Fisers/Weather-station/hardware/Radiation shield/Daniels_Base_Clamp.stl

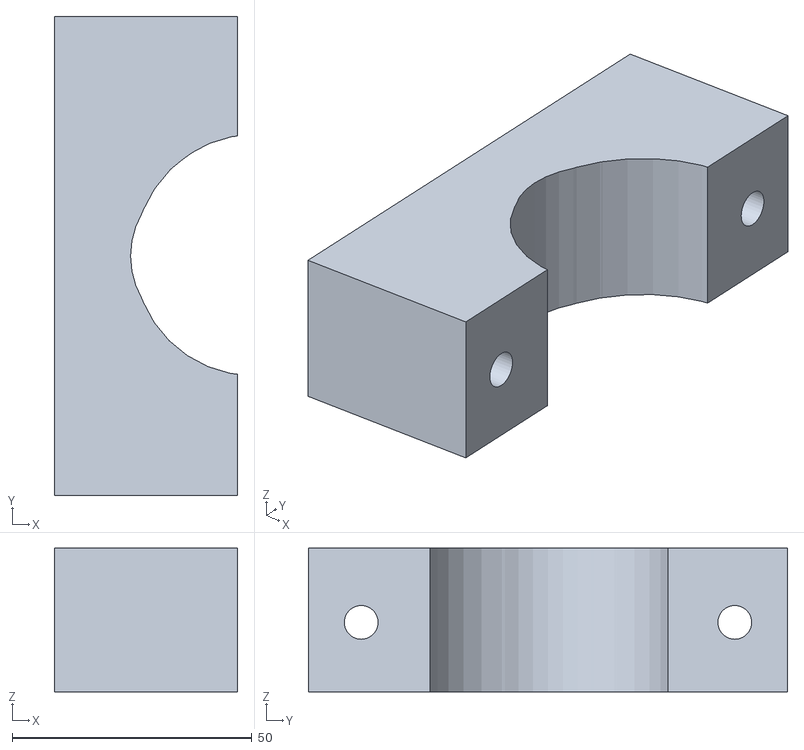
[picture p15: CAD file, 2019-08-27]
hardware/Radiation shield/Daniels_Base_Clamp.stl
38.3 x 100.0 x 30.0
