Fisers/Weather-station/software/Meteorological Station/Meteorological Station/includes/RTC/rtc.c

/***************************************************************************************************
                                   ExploreEmbedded    
****************************************************************************************************
 * File:   rtc.c
 * Version: 15.0
 * Author: ExploreEmbedded
 * Website: http://www.exploreembedded.com/wiki
 * Description: Contains the library functions for RTC-Ds1307 date and time read write

The libraries have been tested on ExploreEmbedded development boards. We strongly believe that the 
library works on any of development boards for respective controllers. However, ExploreEmbedded 
disclaims any kind of hardware failure resulting out of usage of libraries, directly or indirectly.
Files may be subject to change without prior notice. The revision history contains the information 
related to updates. 


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
Errors and omissions should be reported to codelibraries@exploreembedded.com
***************************************************************************************************/



/***************************************************************************************************
                             Revision History
****************************************************************************************************
15.0: Initial version 
***************************************************************************************************/

#include "rtc.h"
#include "../I2C/i2cmaster.h"
#include <util/delay.h>





/***************************************************************************************************
                         void RTC_Init(void)
****************************************************************************************************
 * I/P Arguments: none.
 * Return value    : none

 * description :This function is used to Initialize the Ds1307 RTC.
***************************************************************************************************/
void RTC_Init(void)
{
	rtc_I2C_Start();

    i2c_write(C_Ds1307WriteMode_U8);        // Connect to DS1307 by sending its ID on I2c Bus
    i2c_write(C_Ds1307ControlRegAddress_U8);// Select the Ds1307 ControlRegister to configure Ds1307

    i2c_write(0x00);                        // Write 0x00 to Control register to disable SQW-Out

    i2c_stop();                             // Stop I2C communication after initializing DS1307
}














/***************************************************************************************************
                    void RTC_SetDateTime(rtc_t *rtc)
****************************************************************************************************
 * I/P Arguments: rtc_t *: Pointer to structure of type rtc_t. Structure contains hour,min,sec,day,date,month and year 
 * Return value    : none

 * description  :This function is used to update the Date and time of Ds1307 RTC.
                 The new Date and time will be updated into the non volatile memory of Ds1307.
        Note: The date and time should be of BCD format, 
             like 0x12,0x39,0x26 for 12hr,39min and 26sec.    
                  0x15,0x08,0x47 for 15th day,8th month and 47th year.                 
***************************************************************************************************/
// Convert Decimal to Binary Coded Decimal (BCD)
static uint8_t dec2bcd(uint8_t num)
{
	return ((num/10 * 16) + (num % 10));
}

void RTC_SetDateTime(rtc_t *rtc)
{
    rtc_I2C_Start();                          // Start I2C communication
	
	//i2c_write(0x00);
	//i2c_write(0x80);
    i2c_write(C_Ds1307WriteMode_U8);      // connect to DS1307 by sending its ID on I2c Bus
    i2c_write(C_Ds1307SecondRegAddress_U8); // Request sec RAM address at 00H
	
// 	i2c_write(rtc->sec);                    // Write sec from RAM address 00H
// 	i2c_write(rtc->min);                    // Write min from RAM address 01H
// 	i2c_write(rtc->hour);                    // Write hour from RAM address 02H
// 	i2c_write(rtc->weekDay);                // Write weekDay on RAM address 03H
// 	i2c_write(rtc->date);                    // Write date on RAM address 04H
// 	i2c_write(rtc->month);                    // Write month on RAM address 05H
// 	i2c_write(rtc->year);

    i2c_write(dec2bcd(rtc->sec));                    // Write sec from RAM address 00H
    i2c_write(dec2bcd(rtc->min));                    // Write min from RAM address 01H
    i2c_write(dec2bcd(rtc->hour));                    // Write hour from RAM address 02H
    i2c_write(dec2bcd(rtc->weekDay));                // Write weekDay on RAM address 03H
    i2c_write(dec2bcd(rtc->date));                    // Write date on RAM address 04H
    i2c_write(dec2bcd(rtc->month));                    // Write month on RAM address 05H
    i2c_write(dec2bcd(rtc->year));                    // Write year on RAM address 06h*/

    i2c_stop();                              // Stop I2C communication after Setting the Date
}






// Convert Binary Coded Decimal (BCD) to Decimal
static uint8_t bcd2dec(uint8_t num)
{
	return ((num/16 * 10) + (num % 16));
}


/***************************************************************************************************
                     void RTC_GetDateTime(rtc_t *rtc)
****************************************************************************************************
 * I/P Arguments: rtc_t *: Pointer to structure of type rtc_t. Structure contains hour,min,sec,day,date,month and year 
 * Return value    : none

 * description  :This function is used to get the Date(d,m,y) from Ds1307 RTC.

    Note: The date and time read from Ds1307 will be of BCD format, 
          like 0x12,0x39,0x26 for 12hr,39min and 26sec.    
               0x15,0x08,0x47 for 15th day,8th month and 47th year.              
***************************************************************************************************/
void RTC_GetDateTime(rtc_t *rtc)
{
    rtc_I2C_Start();                            // Start I2C communication

    i2c_write(C_Ds1307WriteMode_U8);        // connect to DS1307 by sending its ID on I2c Bus
    i2c_write(C_Ds1307SecondRegAddress_U8); // Request Sec RAM address at 00H

    i2c_stop();                                // Stop I2C communication after selecting Sec Register
	_delay_ms(100);
    rtc_I2C_Start();                            // Start I2C communication
    i2c_write(C_Ds1307ReadMode_U8);            // connect to DS1307(Read mode) by sending its ID

    rtc->sec = bcd2dec(i2c_readAck());                // read second and return Positive ACK
    rtc->min = bcd2dec(i2c_readAck());                   // read minute and return Positive ACK
    rtc->hour= bcd2dec(i2c_readAck());                  // read hour and return Negative/No ACK
    rtc->weekDay = bcd2dec(i2c_readAck());              // read weekDay and return Positive ACK
    rtc->date= bcd2dec(i2c_readAck());                // read Date and return Positive ACK
    rtc->month=bcd2dec(i2c_readAck());               // read Month and return Positive ACK
    rtc->year =bcd2dec(i2c_readNak());                // read Year and return Negative/No ACK

    i2c_stop();                             // Stop I2C communication after reading the Date
}
