Fisers/Weather-station/software/Meteorological Station/Meteorological Station/includes/UART/uart.c

#define F_CPU 16000000UL // Defining the CPU Frequency for Delay Calculation in delay.h
#define BAUD 9600

#include <avr/io.h>
#include <stdio.h>
#include <util/setbaud.h>
#include "uart.h"

#define _BV(bit) \
(1 << (bit))

#define loop_until_bit_is_set(sfr,bit) \
do { } while (bit_is_clear(sfr, bit))

// UART
void uart_init(void) {
	UBRR0H = UBRRH_VALUE;
	UBRR0L = UBRRL_VALUE;

	#if USE_2X
	UCSR0A |= _BV(U2X0);
	#else
	UCSR0A &= ~(_BV(U2X0));
	#endif

	UCSR0C = _BV(UCSZ01) | _BV(UCSZ00); /* 8-bit data */
	UCSR0B = _BV(RXEN0) | _BV(TXEN0);   /* Enable RX and TX */
}

int uart_putchar(char c, FILE *stream) {
	if (c == '\n') {
		uart_putchar('\r', stream);
	}
	loop_until_bit_is_set(UCSR0A, UDRE0);
	UDR0 = c;
	return 0;
}

int uart_getchar(FILE *stream) {
	loop_until_bit_is_set(UCSR0A, RXC0); /* Wait until data exists. */
	return UDR0;
}
