Fisers/Weather-station/software/Meteorological Station/Meteorological Station/includes/HIH8120/hih8120.h

/*
 * hih8120.h
 *
 * Created: 08/07/2019 13:00:18
 *  Author: daniels
 */ 


#ifndef HIH8120_H_
#define HIH8120_H_


float hih8120_humidity;
float hih8120_temperature_C;

void hih8120_measure();


#endif /* HIH8120_H_ */
